dnewcome/2040-artnode/artnet-led-controller/gen_project.py

#!/usr/bin/env python3
"""Generates artnet-led-controller.kicad_pro"""
import json
from pathlib import Path

DIR = Path(__file__).resolve().parent
PROJ = "artnet-led-controller"

proj = {
    "board": {
        "3dviewports": [],
        "design_settings": {
            "defaults": {
                "board_outline_line_width": 0.05,
                "copper_line_width": 0.25,
                "copper_text_size_h": 1.5,
                "copper_text_size_v": 1.5,
                "copper_text_thickness": 0.3,
                "other_line_width": 0.25,
                "silk_line_width": 0.15,
                "silk_text_size_h": 1.0,
                "silk_text_size_v": 1.0,
                "silk_text_thickness": 0.15
            },
            "rule_severities": {
                "lib_footprint_mismatch": "ignore"
            },
            "rules": {
                "min_clearance": 0.2,
                "min_copper_edge_clearance": 0.3,
                "min_hole_clearance": 0.25,
                "min_hole_to_hole": 0.25,
                "min_microvia_diameter": 0.3,
                "min_microvia_drill": 0.1,
                "min_silk_clearance": 0.0,
                "min_through_hole_diameter": 0.3,
                "min_track_width": 0.2,
                "min_via_annular_width": 0.1,
                "min_via_diameter": 0.6,
                "solder_mask_clearance": 0.05,
                "solder_mask_min_width": 0.0,
                "solder_paste_clearance": 0.0,
                "solder_paste_margin_ratio": 0.0
            }
        },
        "ipc2581": {},
        "layer_presets": [],
        "viewports": []
    },
    "boards": [],
    "cvpcb": {"equivalence_files": []},
    "erc": {"erc_exclusions": [], "meta": {"version": 0}, "pin_map": [], "rule_severities": {}},
    "libraries": {
        "pinned_footprint_libs": [],
        "pinned_symbol_libs": []
    },
    "meta": {"filename": f"{PROJ}.kicad_pro", "version": 1},
    "net_settings": {
        "classes": [
            {
                "bus_width": 12,
                "clearance": 0.2,
                "diff_pair_gap": 0.2,
                "diff_pair_via_gap": 0.2,
                "diff_pair_width": 0.2,
                "line_style": 0,
                "microvia_diameter": 0.3,
                "microvia_drill": 0.1,
                "name": "Default",
                "pcb_color": "rgba(0, 0, 0, 0.000)",
                "schematic_color": "rgba(0, 0, 0, 0.000)",
                "track_width": 0.25,
                "via_diameter": 0.8,
                "via_drill": 0.4,
                "wire_width": 6,
                "bus_width": 12
            },
            {
                "bus_width": 12,
                "clearance": 0.2,
                "diff_pair_gap": 0.2,
                "diff_pair_via_gap": 0.2,
                "diff_pair_width": 0.2,
                "line_style": 0,
                "microvia_diameter": 0.3,
                "microvia_drill": 0.1,
                "name": "Power",
                "pcb_color": "rgba(0, 0, 0, 0.000)",
                "schematic_color": "rgba(0, 0, 0, 0.000)",
                "track_width": 0.5,
                "via_diameter": 0.8,
                "via_drill": 0.4,
                "wire_width": 6,
                "bus_width": 12
            }
        ],
        "meta": {"version": 3},
        "net_colors": None,
        "netclass_assignments": None,
        "netclass_patterns": [
            {"netclass": "Power", "pattern": "VCC*"},
            {"netclass": "Power", "pattern": "GND"},
            {"netclass": "Power", "pattern": "VBAT"},
            {"netclass": "Power", "pattern": "VUSB"},
            {"netclass": "USB",   "pattern": "USB_D*"},
            {"netclass": "ETH",   "pattern": "ETH_*"}
        ]
    },
    "pcbnew": {
        "last_paths": {},
        "page_layout_descr_file": ""
    },
    "schematic": {
        "annotate_start_num": 0,
        "drawing": {
            "default_bus_thickness": 12.0,
            "default_junction_size": 36.0,
            "default_line_thickness": 6.0,
            "default_text_size": 50.0,
            "default_wire_thickness": 6.0,
            "pin_symbol_size": 25.0,
            "text_offset_ratio": 0.08
        },
        "legacy_lib_dir": "",
        "legacy_lib_list": []
    },
    "sheets": [],
    "text_variables": {}
}

out = json.dumps(proj, indent=2)
path = DIR / f"{PROJ}.kicad_pro"
with open(path, 'w') as f:
    f.write(out)
print(f"Project file: {path}")
